gerithebiker/WaxEngineAntiSkateProject/images/withHair.jpg

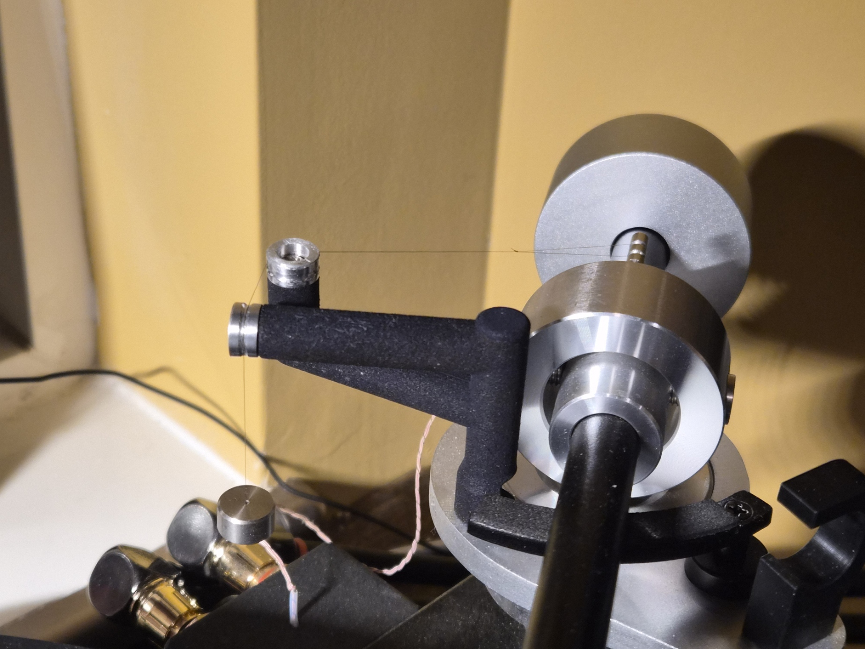
images/withHair.jpg
